BouRHooD/MoscowPolytech_KIAProCeed/Modeling/Blanks_Model/New Дистанционная связь (модуль)/product_add_pic_691.jpg

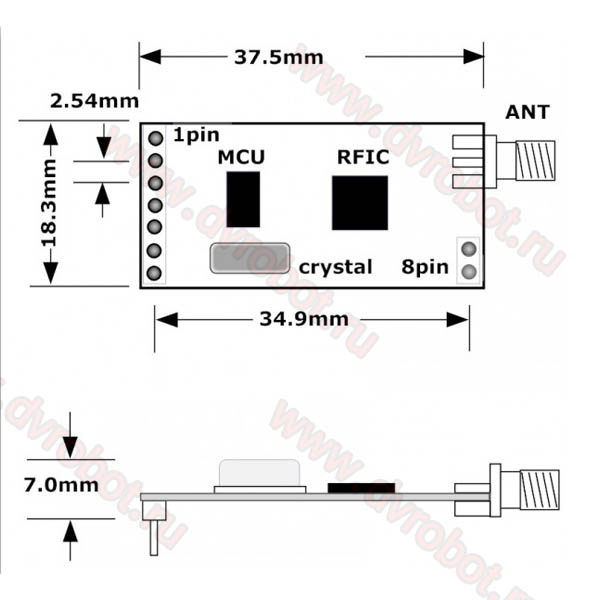
Modeling/Blanks_Model/New Дистанционная связь (модуль)/product_add_pic_691.jpg
