BouRHooD/MoscowPolytech_KIAProCeed/Modeling/Blanks_Model/Газ (модуль)/Screenshot_1.png

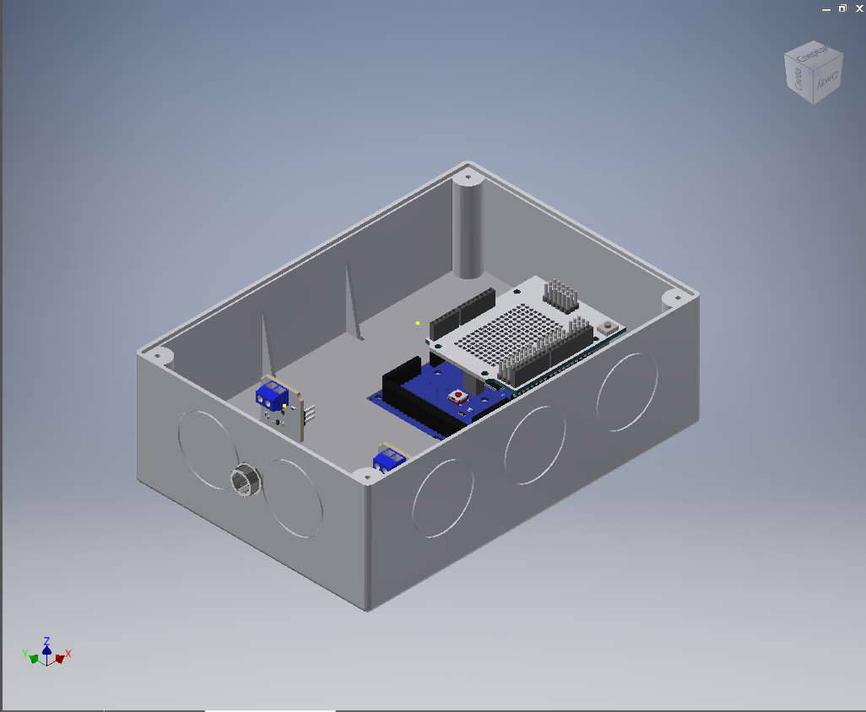
Modeling/Blanks_Model/Газ (модуль)/Screenshot_1.png
