BouRHooD/MoscowPolytech_KIAProCeed/Modeling/Blanks_Model/Газ (модуль)/Screenshot_2.png

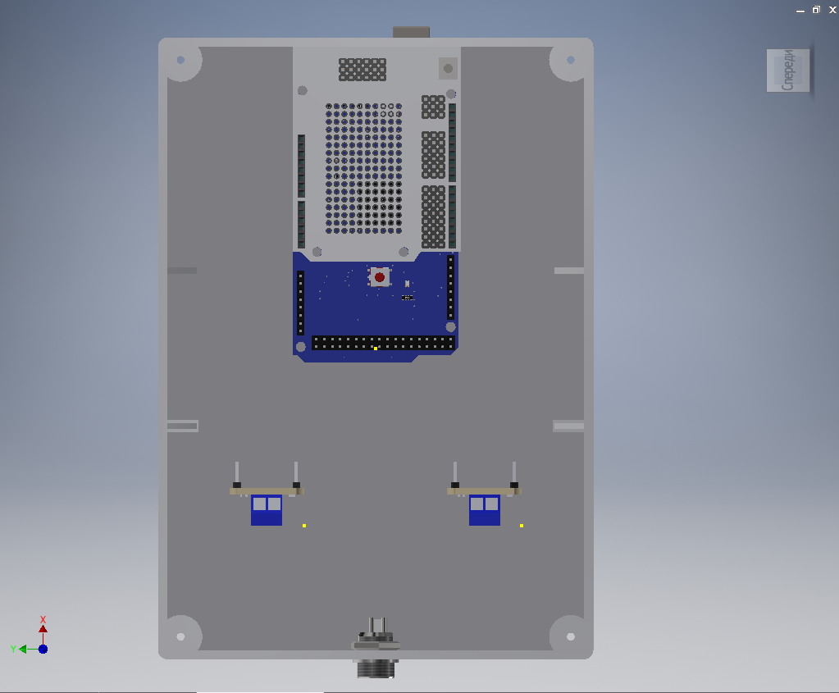
Modeling/Blanks_Model/Газ (модуль)/Screenshot_2.png
