BouRHooD/MoscowPolytech_KIAProCeed/Modeling/Blanks_Model/Газ (модуль)/Screenshot_3.png

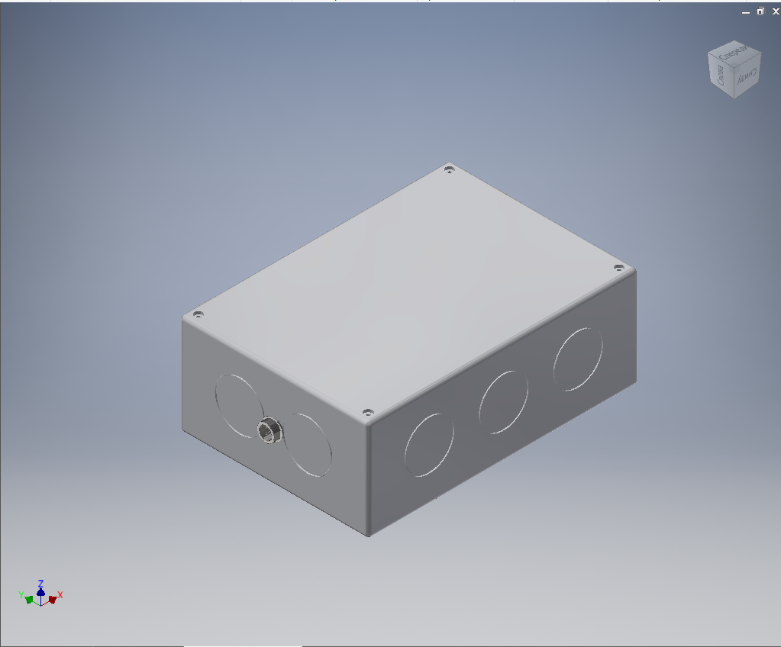
Modeling/Blanks_Model/Газ (модуль)/Screenshot_3.png
