BouRHooD/MoscowPolytech_KIAProCeed/Modeling/Blanks_Model/Газ (модуль)/Screenshot_5.png

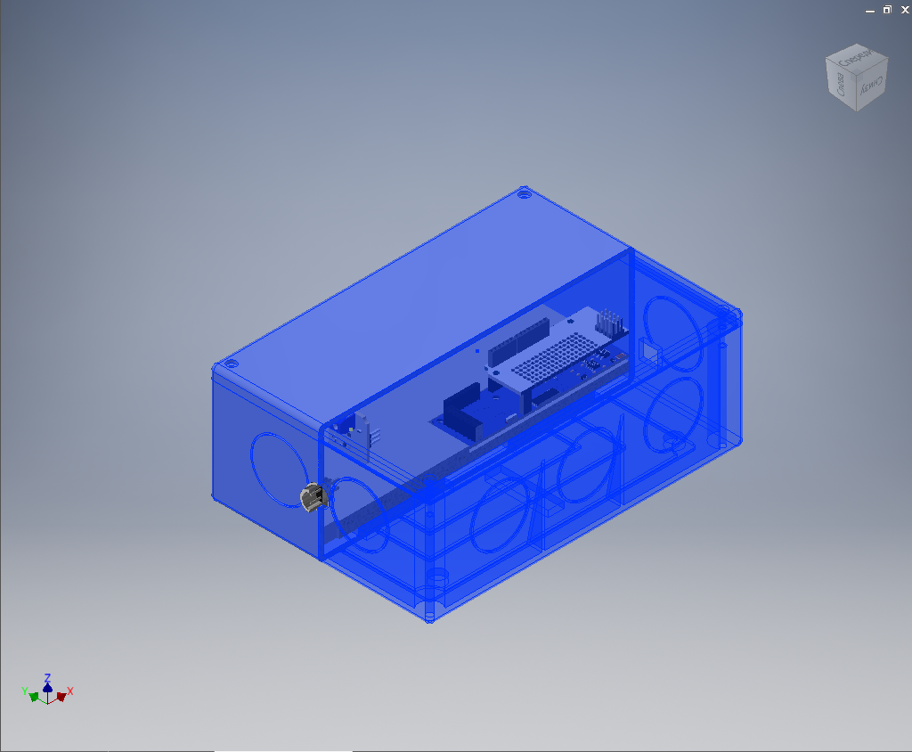
Modeling/Blanks_Model/Газ (модуль)/Screenshot_5.png
