BouRHooD/MoscowPolytech_KIAProCeed/Modeling/Power_supply_Car_Model/Фото/_1.png

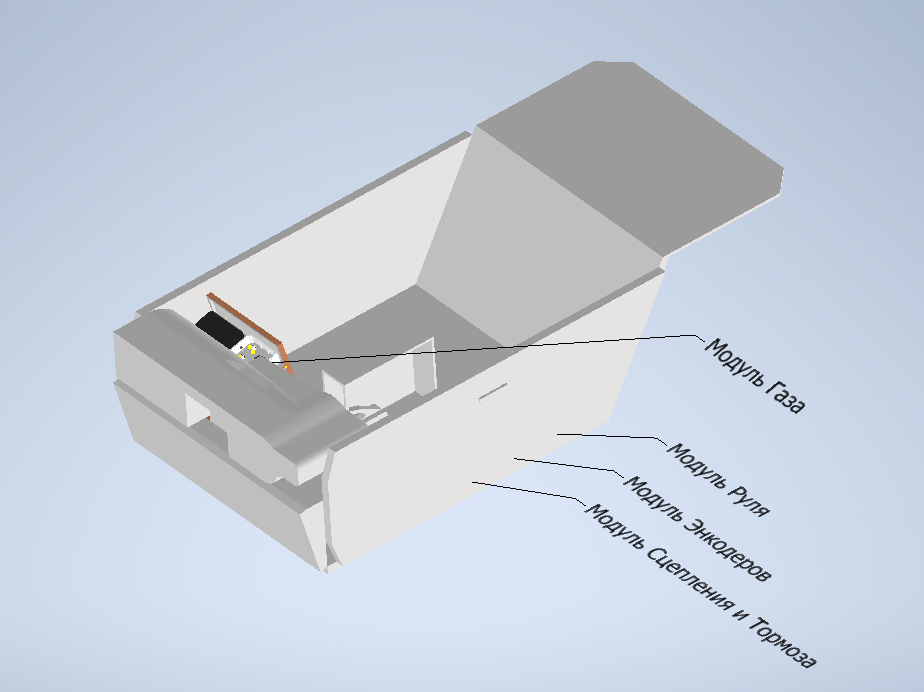
Modeling/Power_supply_Car_Model/Фото/_1.png
