BouRHooD/MoscowPolytech_KIAProCeed/Modeling/Power_supply_Car_Model/Фото/_3.png

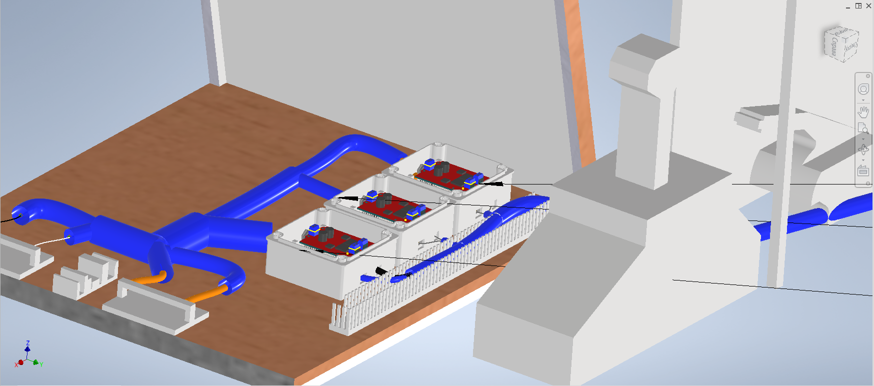
Modeling/Power_supply_Car_Model/Фото/_3.png
