BouRHooD/MoscowPolytech_KIAProCeed/Modeling/Power_supply_Car_Model/Фото/_4.png

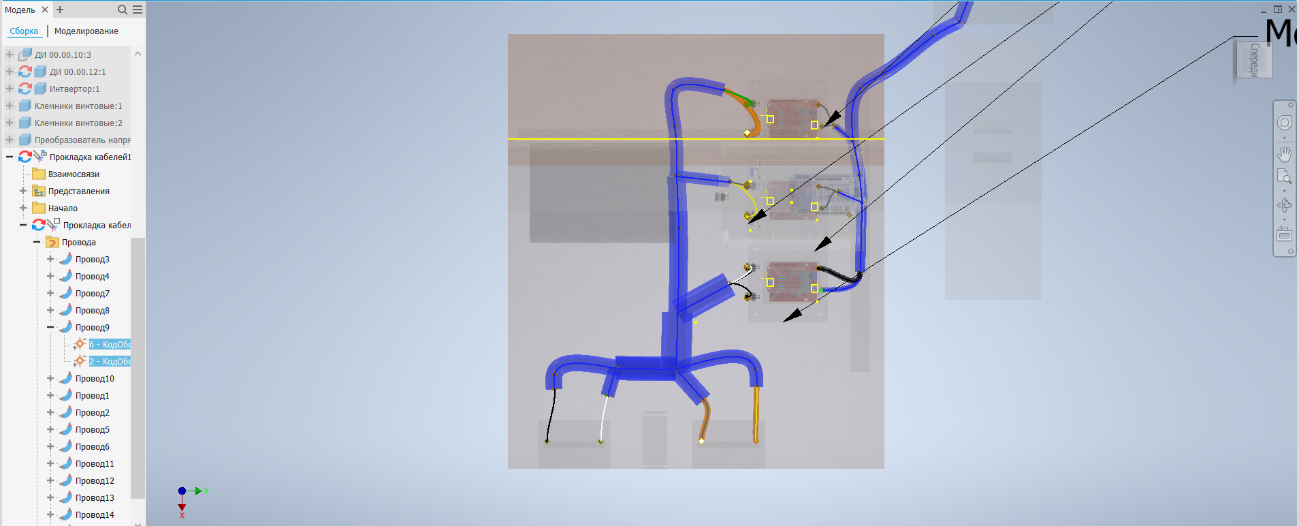
Modeling/Power_supply_Car_Model/Фото/_4.png
