BouRHooD/MoscowPolytech_KIAProCeed/Modeling/Power_supply_Car_Model/Фото/_7.png

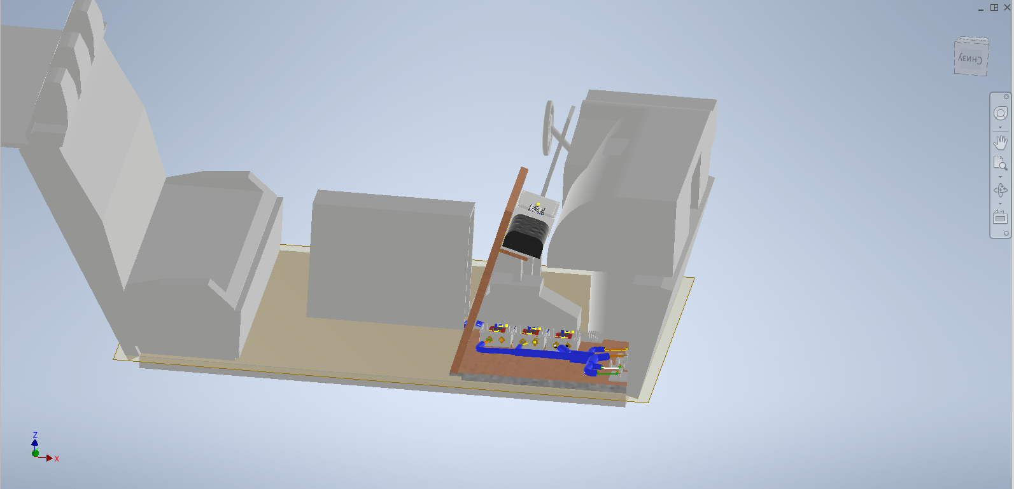
Modeling/Power_supply_Car_Model/Фото/_7.png
