BouRHooD/MoscowPolytech_KIAProCeed/Windows Programm/Control_Board_Kia_ProCeed/WindowsFormsMotionPath/Скриншоты/ScreenshotApp_4.png

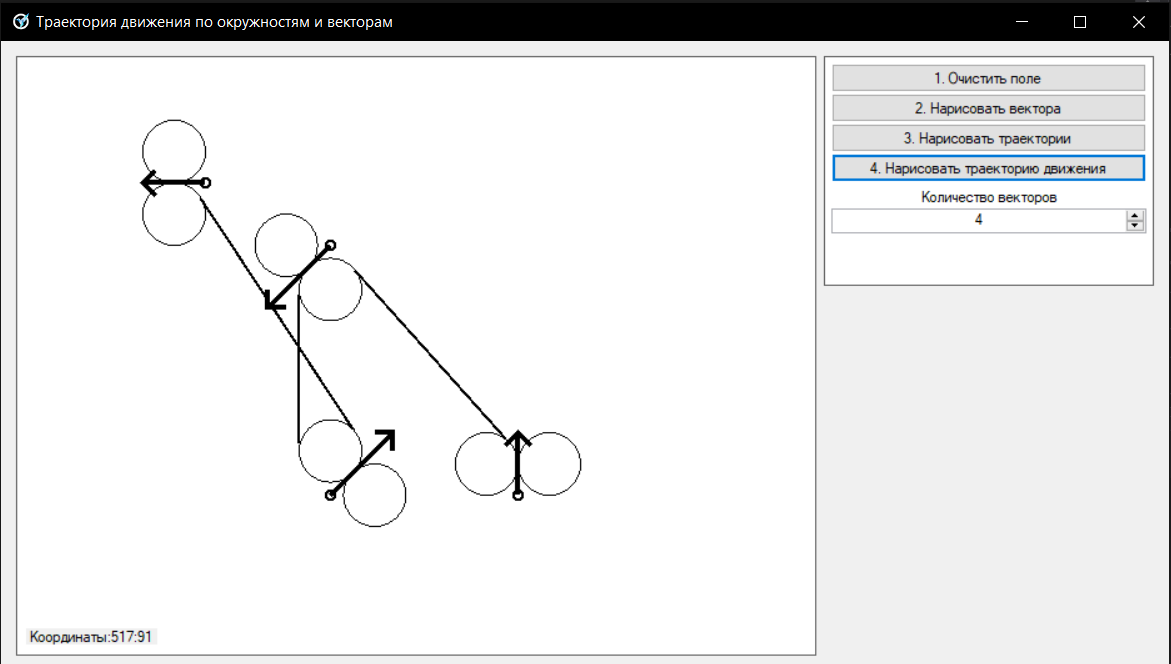
Windows Programm/Control_Board_Kia_ProCeed/WindowsFormsMotionPath/Скриншоты/ScreenshotApp_4.png
